gurues/Crono_Arena/Ayuda/01_Cronometro-Arena.jpg

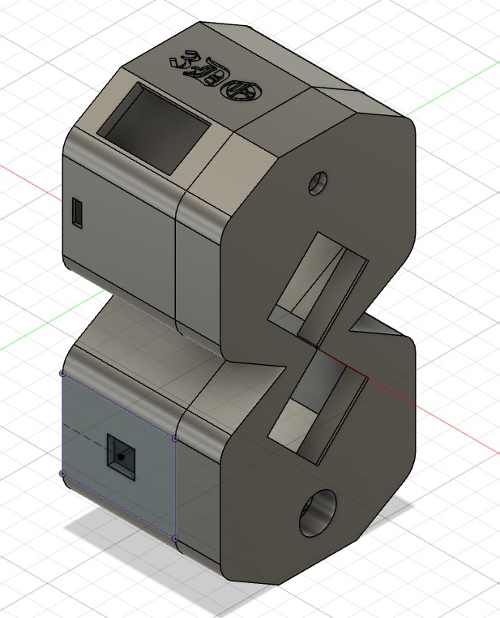
Ayuda/01_Cronometro-Arena.jpg
