gurues/Crono_Arena/Ayuda/03_Cronometro-Arena.jpg

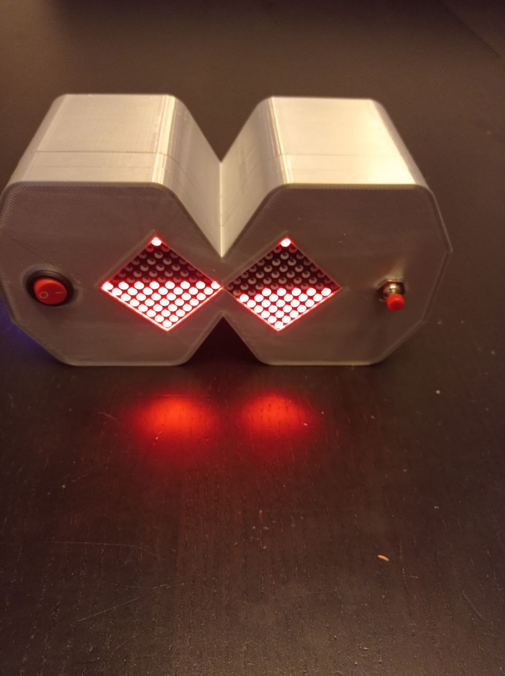
Ayuda/03_Cronometro-Arena.jpg
