gurues/Crono_Arena/Ayuda/06_Cronometro-Arena.jpg

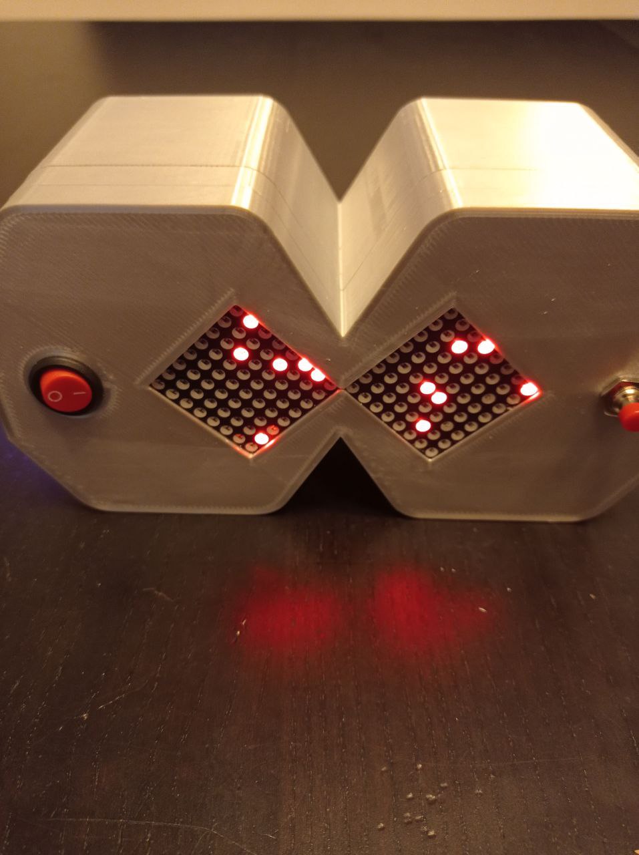
Ayuda/06_Cronometro-Arena.jpg
