gurues/Crono_Arena/Ayuda/08_Cronometro-Arena.jpg

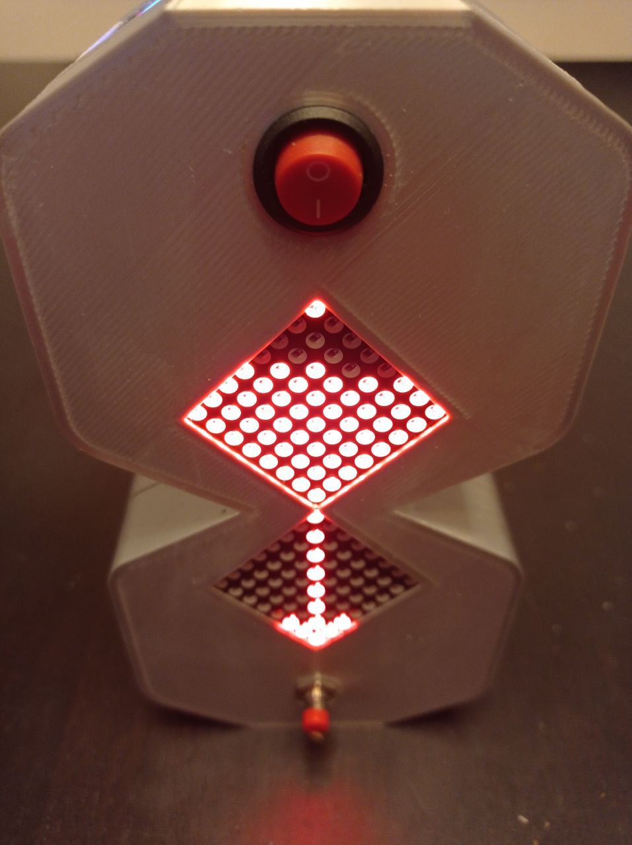
Ayuda/08_Cronometro-Arena.jpg
